heimdallngenuitysd-lang/heimdall-liquid-handler/Hardware/3D Printing Files/Holder for 15ml Falcon tubes and 2ml Centrifuge tubes.stl

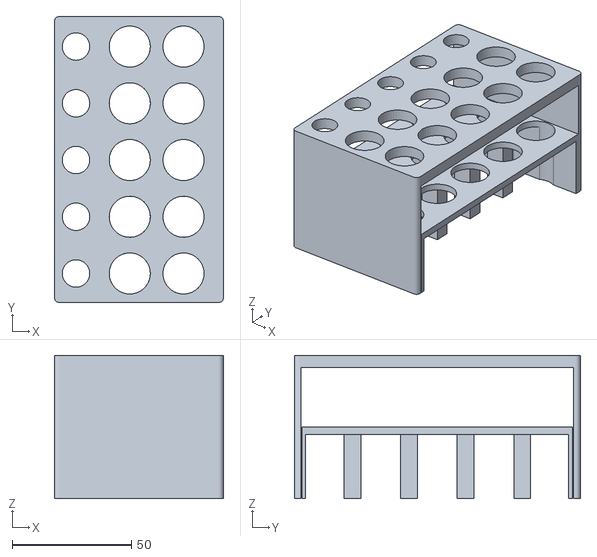
[picture p15: CAD file, 2026-09-15]
Hardware/3D Printing Files/Holder for 15ml Falcon tubes and 2ml Centrifuge tubes.stl
70.8 x 119.8 x 60.0
